FirstTestStation/InterconnectIO_Board/InterconnectIO_bd/DOC/FirstTestStation.jpg

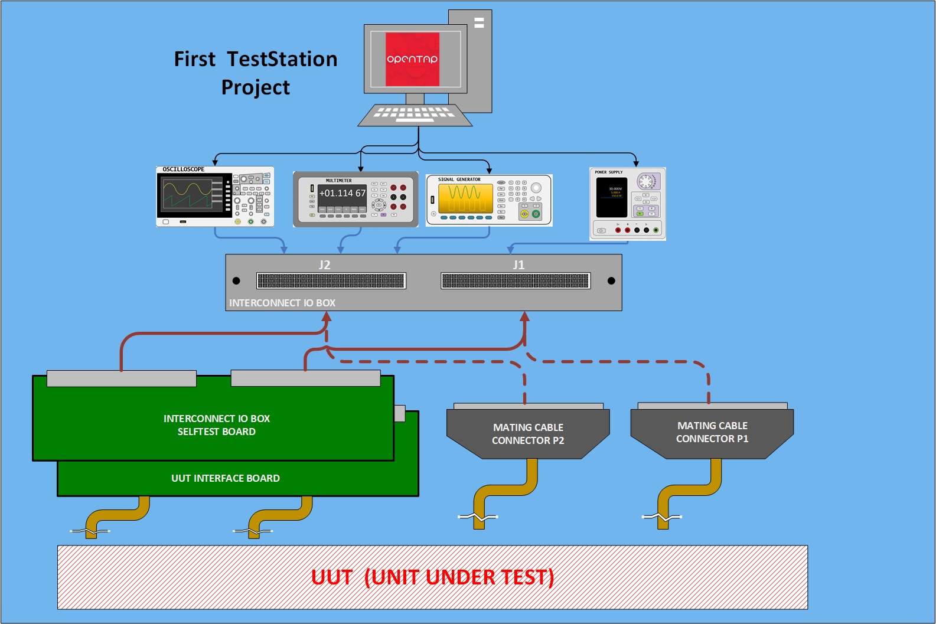
InterconnectIO_bd/DOC/FirstTestStation.jpg
